strickinato/ledriver/ledriver_firmware/LrBuffer.cpp

#include "LrBuffer.h"

LrBuffer::LrBuffer(){
    memset(drawBuffer, 0,  sizeof(drawBuffer));
    ledCount = LR_NUM_LEDS;
    ledsEnabled = false;
}

void LrBuffer::begin(){
    leds = (CRGB *)drawBuffer;
    // #if OCTOWSMODE
    //     LEDS.addLeds<OCTOWS2811>(leds, LR_LED_PER_STRIP);
    // #else
    //     FastLED.addLeds<LED_TYPE, DATA_PIN, GRB>(leds, LR_NUM_LEDS);
    // #endif
    // FastLED.setDither( 0 );
    // FastLED.show();
}

void LrBuffer::enableFastLED(const uint8_t _ledOuputType, const uint8_t _colorOrder){//uint8_t _mode){
    ledsEnabled = true;
    if (_ledOuputType == FAST_WS2801) {
        // either implement color order in switch case here or in software
        // Serial.println("yes set to ws2801");
        FastLED.addLeds<WS2801, DATA_PIN, CLOCK_PIN, BRG>(leds, LR_NUM_LEDS);
    }
    else if (_ledOuputType == FAST_OCTO){
        #if OCTOWSMODE
            LEDS.addLeds<OCTOWS2811>(leds, LR_LED_PER_STRIP);
        #else
            Serial.println("fastocto not enabled, please compile with");
        #endif
    }

    FastLED.setDither( 0 );
    FastLED.show();
}

CRGB * LrBuffer::getLEDs(){
    return leds;
}

uint8_t * LrBuffer::getDMX(uint8_t _u){
    if(_u == 0){
        return drawBuffer + LR_NUM_LEDS*3;
    }
    else {
        return drawBuffer + LR_NUM_LEDS*3 + 512;
    }
}

void LrBuffer::show(){
    if(ledsEnabled){
        FastLED.show();
    }
}
